asterix24/nixi-clock/hardware/kicad/main.kicad_sch

## KiCad design hardware/kicad/main.kicad_sch (2026-05-16)

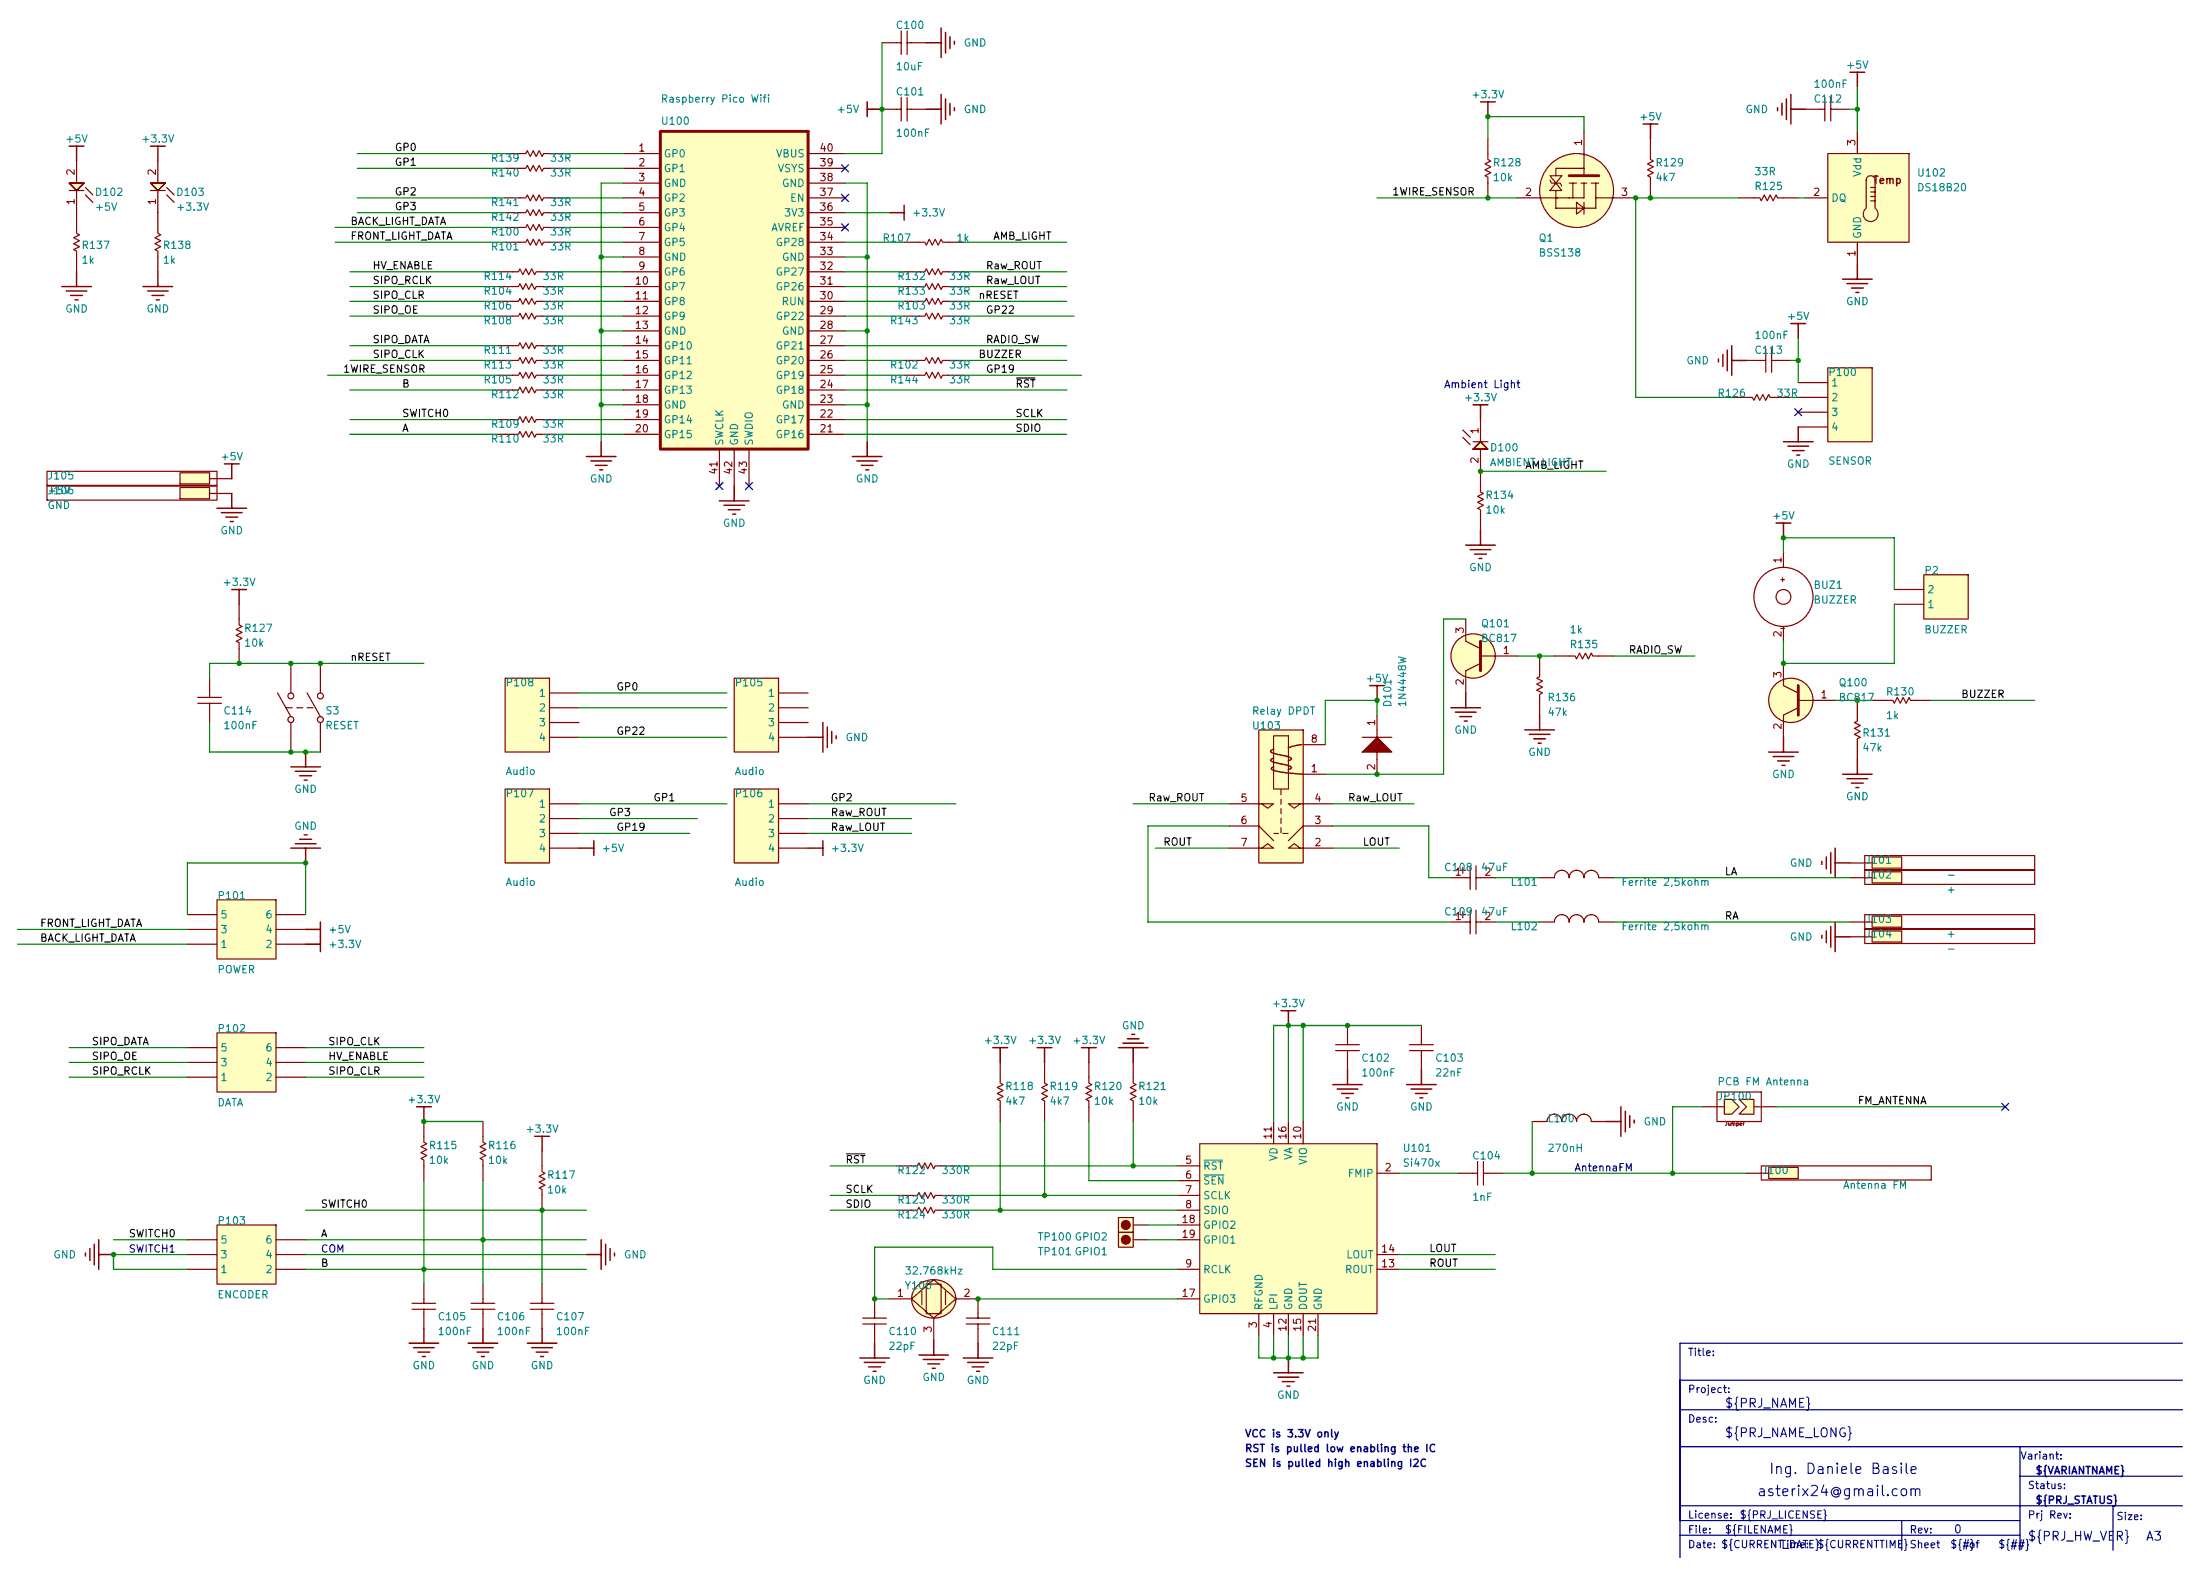
[picture p26: schematic main.kicad_sch]

Parts:
BUZ1: BUZZER; buzzer_14mm_thd
C100: 10uF; 0603_[1608]
C101, C102, C105, C106, C107, C112, C113, C114: 100nF; 0603_[1608]
C103: 22nF; 0603_[1608]
C104: 1nF; 0603_[1608]
C108, C109: 47uF; [7343]_CAP_TAN_1P_2N
C110, C111: 22pF; 0603_[1608]
D100: AMBIENT LIGHT; R5_LED_THD_A2-K1
D101: 1N4448W; SOD-123_K1-A2
D102: +5V; 0603_[1608]_K1-A2_LED
D103: +3.3V; 0603_[1608]_K1-A2_LED
J100: Antenna FM; SMD_PIN_2x5MM
J101, J104: -; SMD_PIN_2x5MM
J102, J103: +; SMD_PIN_2x5MM
J105: +5V; SMD_PIN_2x5MM
J106: GND; SMD_PIN_2x5MM
JP100: PCB FM Antenna; 0603_[1608]_JUMPER
L100: 270nH; 0603_[1608]
L101, L102: Ferrite 2,5kohm; 0603_[1608]
P2: BUZZER; HEADER_1X2_2.54MM_THD
P100: SENSOR; HEADER_1X4_2.54MM_THD
P101: POWER; SOCKET_2x3_2.54mm_THD
P102: DATA; SOCKET_2x3_2.54mm_THD
P103: ENCODER; SOCKET_2x3_2.54mm_THD
P105, P106, P107, P108: Audio; HEADER_1X4_2.54MM_THD
Q1: BSS138; SOT-23
Q100, Q101: BC817; SOT-23
R100, R101, R102, R103, R104, R105, R106, R108, R109, R110, R111, R112, R113, R114, R125, R126, R132, R133, R139, R140, R141, R142, R143, R144: 33R; 0603_[1608]
R107, R130, R135, R137, R138: 1k; 0603_[1608]
R115, R116, R117, R120, R121, R127, R128, R134: 10k; 0603_[1608]
R118, R119, R129: 4k7; 0603_[1608]
R122, R123, R124: 330R; 0603_[1608]
R131, R136: 47k; 0603_[1608]
S3: RESET; TACTILE_SWITCH_6x6MM_THD
TP100: GPIO2; TEST_POINT_THD_D1.6MM
TP101: GPIO1; TEST_POINT_THD_D1.6MM
U100: Raspberry Pico Wifi; RasberryPicoMod
U101: Si470x; QFN-50P-20_PAD
U102: DS18B20; TO-92
U103: Relay DPDT; RELAYS_DPST_THD_6x10_5.08mm
Y100: 32.768kHz; CRISTAL_R26_PAD

Connections:
1WIRE_SENSOR: Q1.2 (S), R105.2, R128.2
A: C106.2, P103.6, R110.2, R116.2
AMB_LIGHT: D100.2 (A), R107.1, R134.1
B: C105.2, P103.2, R112.2, R115.2
BACK_LIGHT_DATA: P101.1, R100.2
BUZZER: R102.1, R130.1
FM_ANTENNA: JP100.2
FRONT_LIGHT_DATA: P101.3, R101.2
GP0: P108.1, R139.2
GP1: P107.1, R140.2
GP2: P106.1, R141.2
GP3: P107.2, R142.2
GP19: P107.3, R144.1
GP22: P108.4, R143.1
HV_ENABLE: P102.4, R114.2
LA: J102.1, L101.2
LOUT: U101.14 (LOUT), U103.2
unnamed: BUZ1.1, P2.2
unnamed: BUZ1.2, P2.1, Q100.3
unnamed: C100.1, C101.1, U100.40 (VBUS)
unnamed: C102.2, C103.2, U101.10 (VIO), U101.11 (VD), U101.16 (VA)
unnamed: C104.1, U101.2 (FMIP)
unnamed: C104.2, J100.1, JP100.1, L100.1
unnamed: C108.1, U103.3
unnamed: C108.2, L101.1
unnamed: C109.1, U103.6
unnamed: C109.2, L102.1
unnamed: C110.2, U101.9 (RCLK), Y100.1
unnamed: C111.2, U101.17 (GPIO3), Y100.2
unnamed: C112.1, U102.3 (Vdd)
unnamed: C113.1, P100.1
unnamed: C114.1, S3.1 (COMMON1), S3.2 (COMMON2)
unnamed: D101.1 (K), U103.8
unnamed: D101.2 (A), Q101.3, U103.1 (T1)
unnamed: D102.1 (K), R137.2
unnamed: D103.1 (K), R138.2
unnamed: P100.2, R126.1
unnamed: P101.5, P101.6
unnamed: P103.1, P103.3
unnamed: Q1.1 (G), R128.1
unnamed: Q1.3 (D), R125.2, R126.2, R129.2
unnamed: Q100.1, R130.2, R131.2
unnamed: Q101.1, R135.2, R136.2
unnamed: R100.1, U100.6 (GP4)
unnamed: R101.1, U100.7 (GP5)
unnamed: R102.2, U100.26 (GP20)
unnamed: R103.2, U100.30 (RUN)
unnamed: R104.1, U100.10 (GP7)
unnamed: R105.1, U100.16 (GP12)
unnamed: R106.1, U100.11 (GP8)
unnamed: R107.2, U100.34 (GP28)
unnamed: R108.1, U100.12 (GP9)
unnamed: R109.1, U100.19 (GP14)
unnamed: R110.1, U100.20 (GP15)
unnamed: R111.1, U100.14 (GP10)
unnamed: R112.1, U100.17 (GP13)
unnamed: R113.1, U100.15 (GP11)
unnamed: R114.1, U100.9 (GP6)
unnamed: R115.1, R116.1
unnamed: R118.2, R124.1, U101.8 (SDIO)
unnamed: R119.2, R123.1, U101.7 (SCLK)
unnamed: R120.2, U101.6 (~SEN)
unnamed: R121.2, R122.1, U101.5 (~RST)
unnamed: R125.1, U102.2 (DQ)
unnamed: R132.2, U100.32 (GP27)
unnamed: R133.2, U100.31 (GP26)
unnamed: R139.1, U100.1 (GP0)
unnamed: R140.1, U100.2 (GP1)
unnamed: R141.1, U100.4 (GP2)
unnamed: R142.1, U100.5 (GP3)
unnamed: R143.2, U100.29 (GP22)
unnamed: R144.2, U100.25 (GP19)
unnamed: TP100.1, U101.18 (GPIO2)
unnamed: TP101.1, U101.19 (GPIO1)
unnamed: U100.3 (GND), U100.8 (GND), U100.13 (GND), U100.18 (GND)
unnamed: U100.23 (GND), U100.28 (GND), U100.33 (GND), U100.38 (GND)
unnamed: U101.3 (RFGND), U101.4 (LPI), U101.12 (GND), U101.15 (DOUT), U101.21 (GND)
RA: J103.1, L102.2
RADIO_SW: R135.1, U100.27 (GP21)
ROUT: U101.13 (ROUT), U103.7
Raw_LOUT: P106.3, R133.1, U103.4
Raw_ROUT: P106.2, R132.1, U103.5
SCLK: R123.2, U100.22 (GP17)
SDIO: R124.2, U100.21 (GP16)
SIPO_CLK: P102.6, R113.2
SIPO_CLR: P102.2, R106.2
SIPO_DATA: P102.5, R111.2
SIPO_OE: P102.3, R108.2
SIPO_RCLK: P102.1, R104.2
SWITCH0: C107.2, P103.5, R109.2, R117.2
nRESET: C114.2, R103.1, R127.2, S3.3 (NO1), S3.4 (NO2)
~RST: R122.2, U100.24 (GP18)

Notes on the sheet:
${##}
COM
VCC is 3.3V only
asterix24@gmail.com
${#}
${REVISION}
Sheet
${CURRENT_DATE}
${PRJ_LICENSE}
${VARIANTNAME}
File:
Project:
SEN is pulled high enabling I2C
${FILENAME}
Ing. Daniele Basile
AntennaFM
${PRJ_NAME}
Status:
Variant:
Desc:
${PRJ_NAME_LONG}
Date:
SWITCH1
${TITLE}
${CURRENTTIME}
Title:
Time:
Ambient Light
${PRJ_STATUS}
Size:
Rev:
RST is pulled low enabling the IC
Prj Rev:
${PRJ_HW_VER}
License:
