asterix24/nixi-clock/hardware/kicad/supply.kicad_sch

## KiCad design hardware/kicad/supply.kicad_sch (2026-05-16)

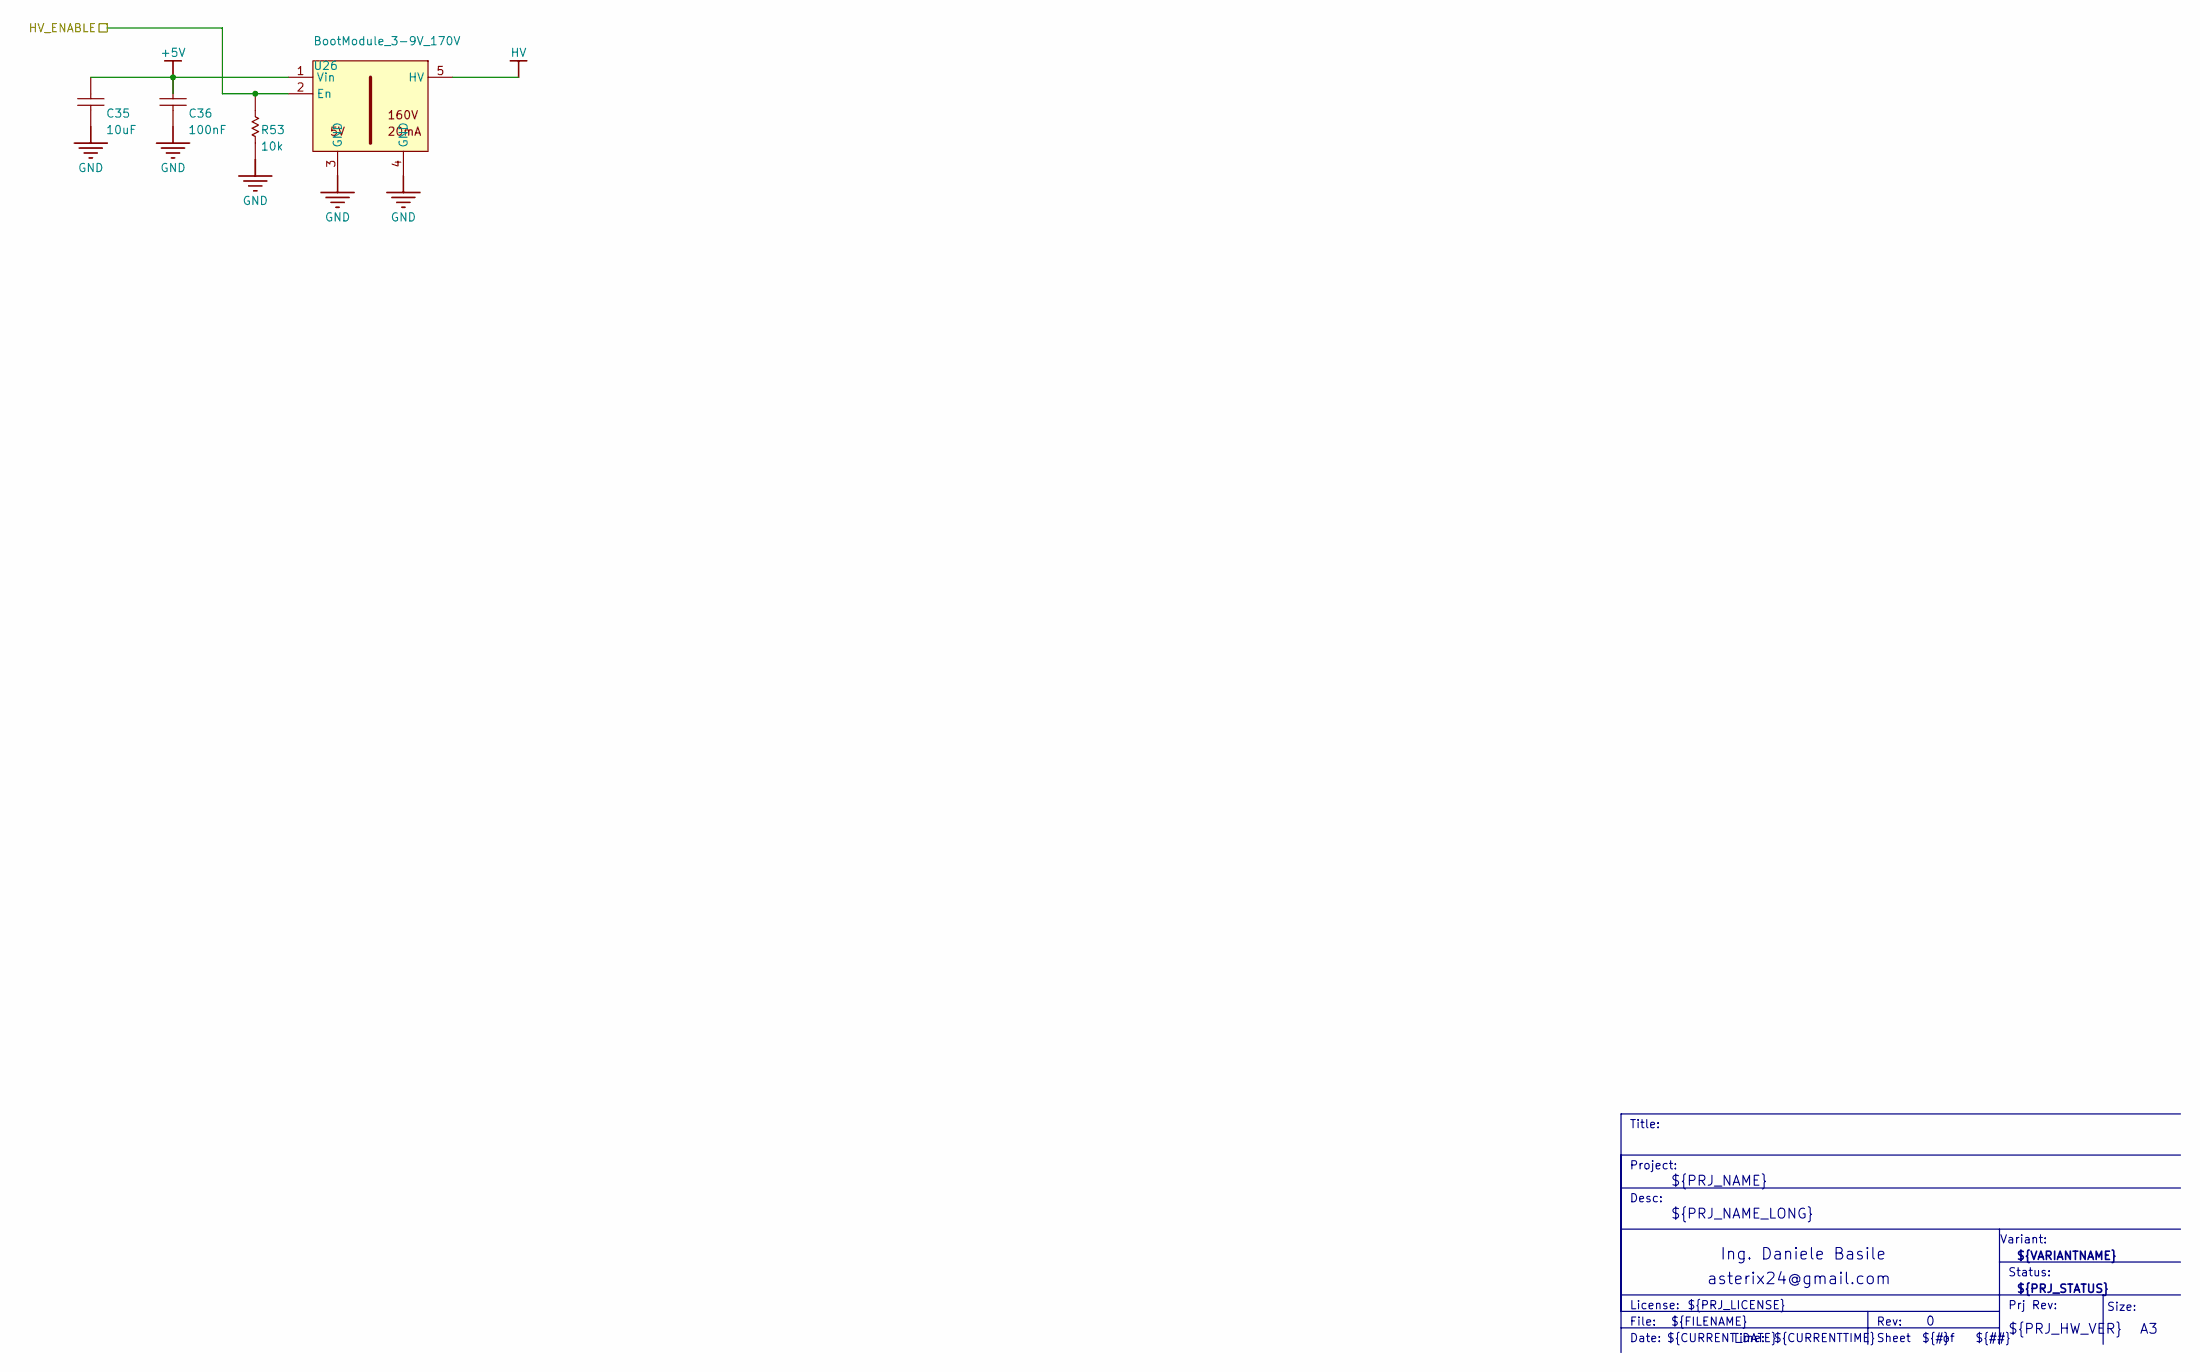
[picture p27: schematic supply.kicad_sch]

Parts:
C35: 10uF; 0603_[1608]
C36: 100nF; 0603_[1608]
R53: 10k; 0603_[1608]
U26: BootModule_3-9V_170V; BoostModule

Connections:
HV_ENABLE: R53.2, U26.2 (En)
unnamed: C35.2, C36.2, U26.1 (Vin)

Notes on the sheet:
${PRJ_NAME}
Desc:
${PRJ_LICENSE}
Date:
${##}
Size:
Rev:
${PRJ_NAME_LONG}
License:
${PRJ_HW_VER}
Sheet
${FILENAME}
${CURRENT_DATE}
Variant:
${REVISION}
${PRJ_STATUS}
${#}
Ing. Daniele Basile
asterix24@gmail.com
${VARIANTNAME}
Time:
Project:
Title:
${TITLE}
File:
Prj Rev:
Status:
${CURRENTTIME}
