asterix24/nixi-clock/hardware/kicad/tube.kicad_sch

## KiCad design hardware/kicad/tube.kicad_sch (2026-05-16)

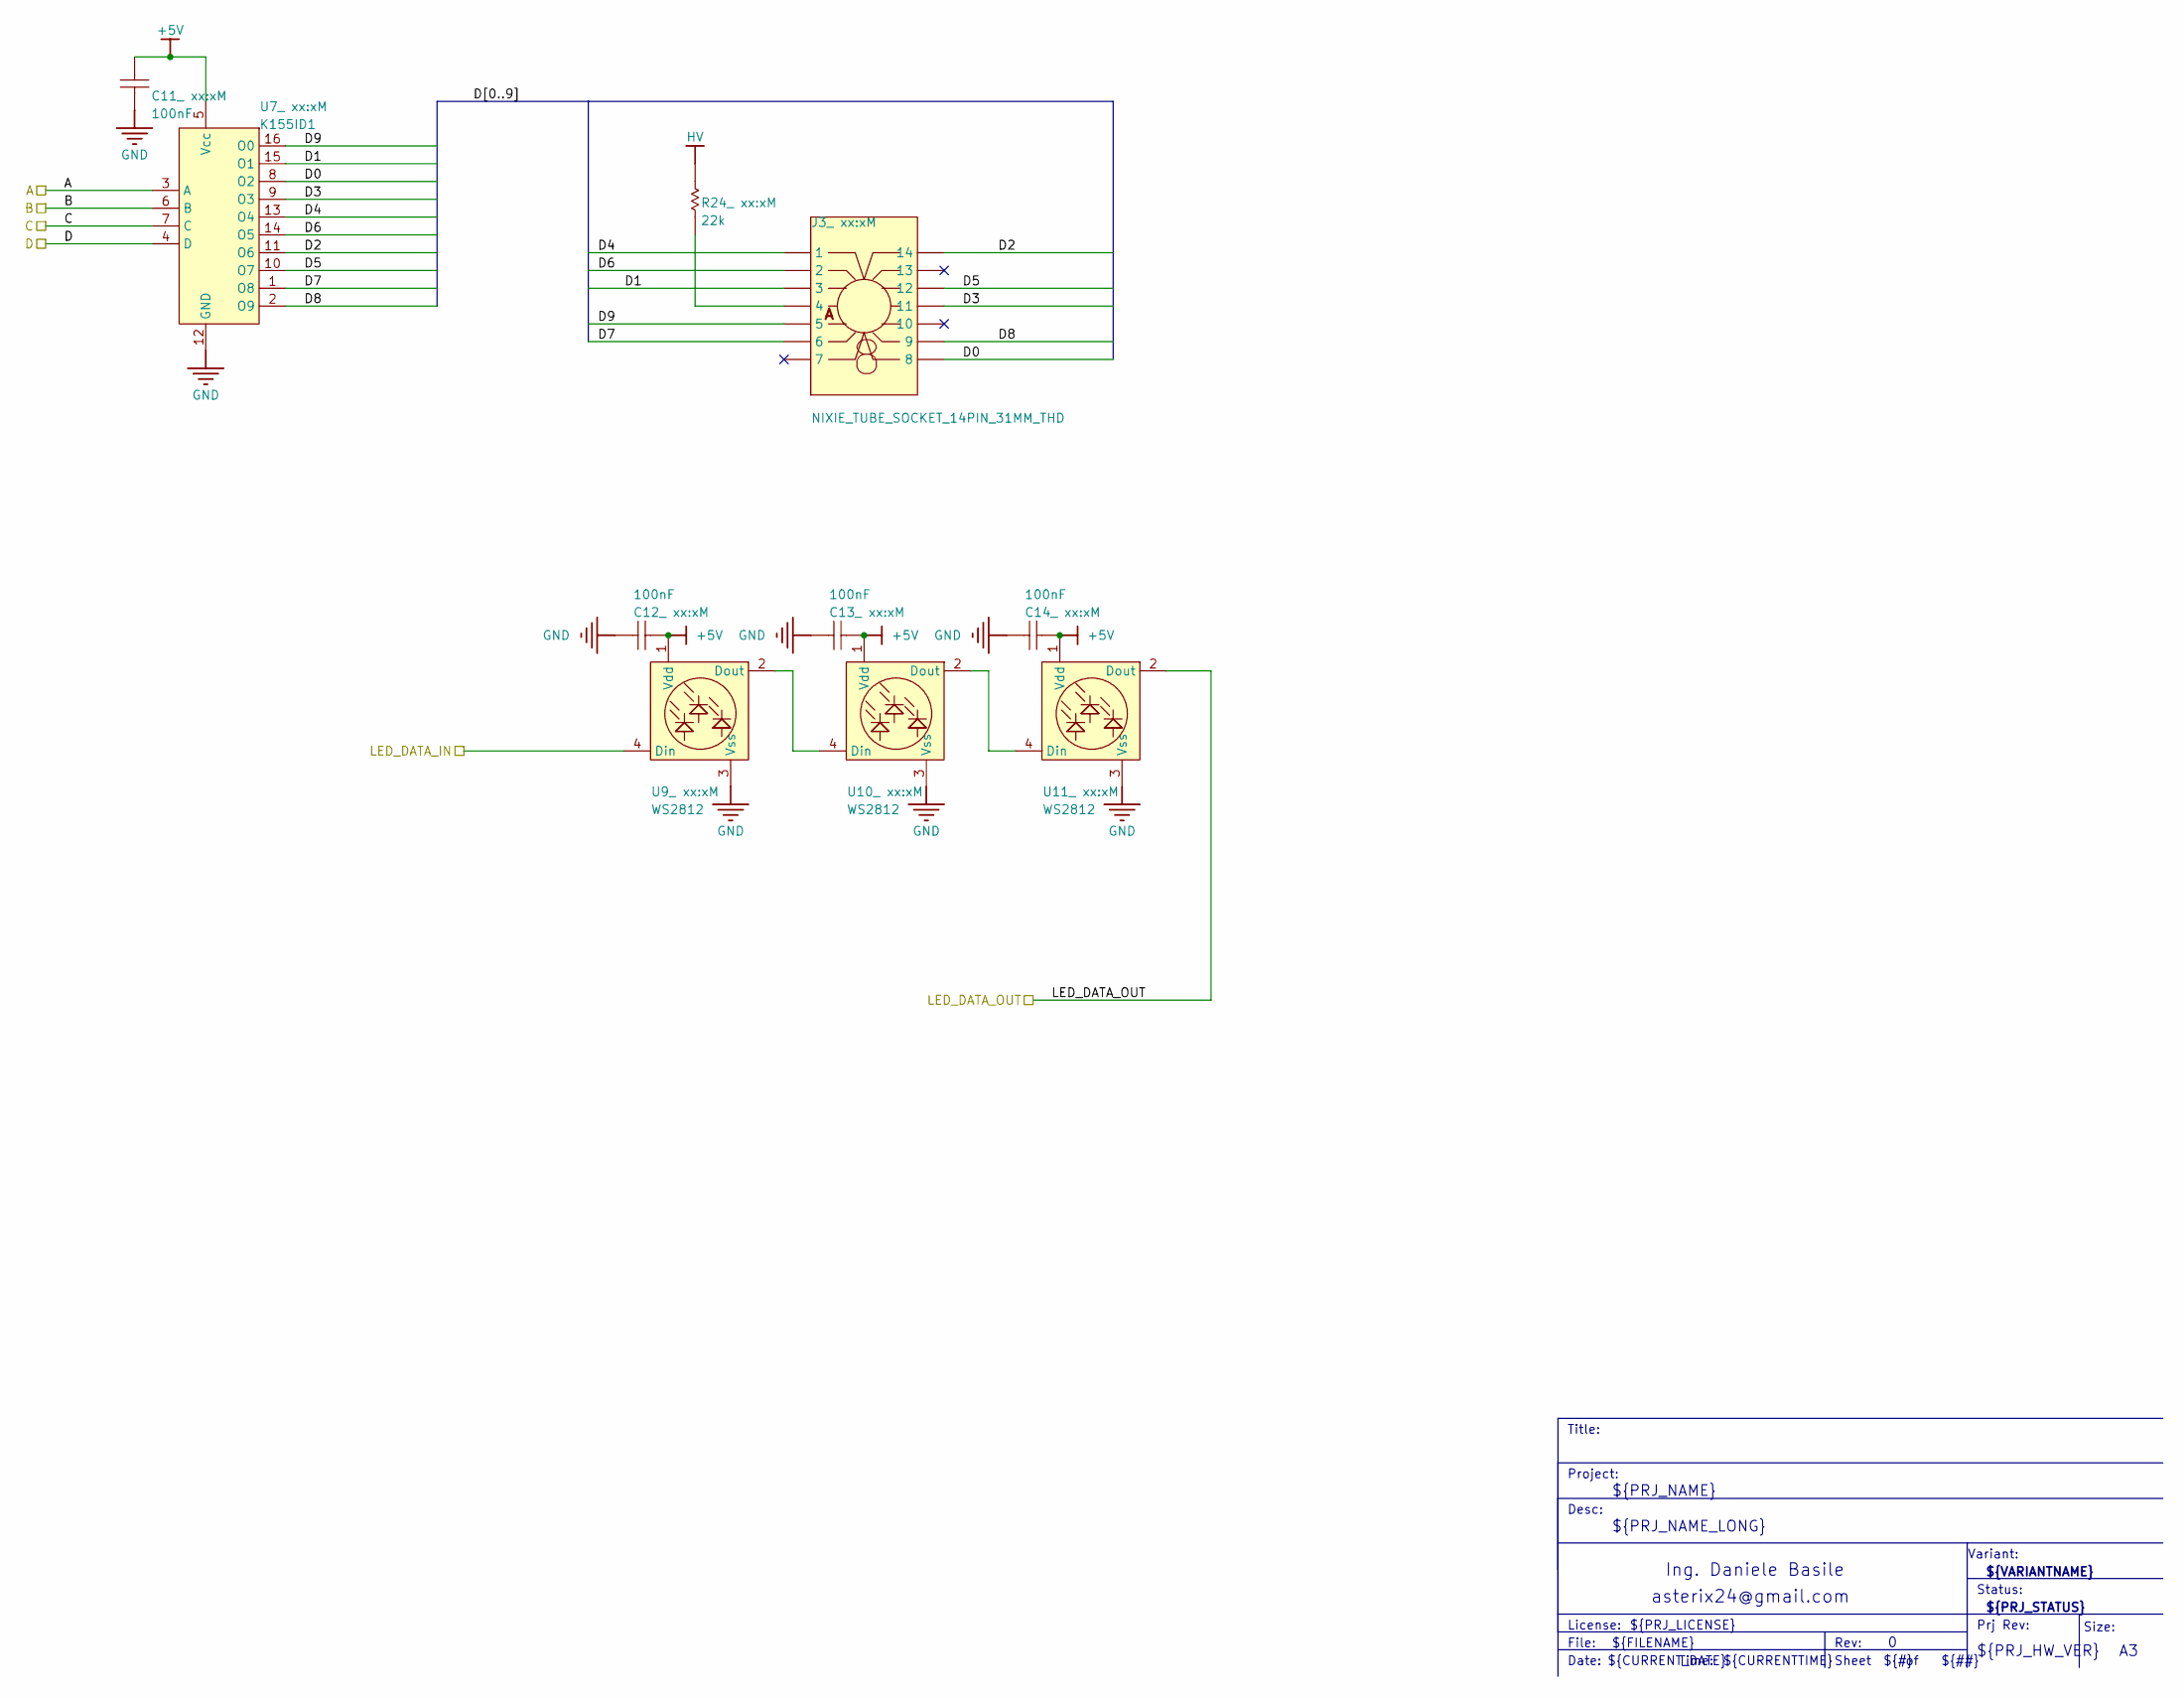
[picture p28: schematic tube.kicad_sch]

Parts:
C11_ xx:xM, C12_ xx:xM, C13_ xx:xM, C14_ xx:xM: 100nF; 0603_[1608]
J3_ xx:xM: NIXIE_TUBE_SOCKET_14PIN_31MM_THD; SOCKET_NIXI_TUBE
R24_ xx:xM: 22k; AXIAL 10mm
U7_ xx:xM: K155ID1; DIP-16_THD
U9_ xx:xM, U10_ xx:xM, U11_ xx:xM: WS2812; LED_PLCC_RGB_4P_1010

Connections:
A: U7_ xx:xM.3 (A)
B: U7_ xx:xM.6 (B)
C: U7_ xx:xM.7 (C)
D: U7_ xx:xM.4 (D)
D0: J3_ xx:xM.8, U7_ xx:xM.8 (O2)
D1: J3_ xx:xM.3, U7_ xx:xM.15 (O1)
D2: J3_ xx:xM.14, U7_ xx:xM.11 (O6)
D3: J3_ xx:xM.11, U7_ xx:xM.9 (O3)
D4: J3_ xx:xM.1, U7_ xx:xM.13 (O4)
D5: J3_ xx:xM.12, U7_ xx:xM.10 (O7)
D6: J3_ xx:xM.2, U7_ xx:xM.14 (O5)
D7: J3_ xx:xM.6, U7_ xx:xM.1 (O8)
D8: J3_ xx:xM.9, U7_ xx:xM.2 (O9)
D9: J3_ xx:xM.5, U7_ xx:xM.16 (O0)
LED_DATA_IN: U9_ xx:xM.4 (Din)
LED_DATA_OUT: U11_ xx:xM.2 (Dout)
unnamed: C11_ xx:xM.2, U7_ xx:xM.5 (Vcc)
unnamed: C12_ xx:xM.2, U9_ xx:xM.1 (Vdd)
unnamed: C13_ xx:xM.2, U10_ xx:xM.1 (Vdd)
unnamed: C14_ xx:xM.2, U11_ xx:xM.1 (Vdd)
unnamed: J3_ xx:xM.4, R24_ xx:xM.1
unnamed: U10_ xx:xM.2 (Dout), U11_ xx:xM.4 (Din)
unnamed: U9_ xx:xM.2 (Dout), U10_ xx:xM.4 (Din)

Notes on the sheet:
asterix24@gmail.com
File:
${REVISION}
License:
Title:
Desc:
${CURRENTTIME}
${PRJ_LICENSE}
${TITLE}
Prj Rev:
Variant:
${CURRENT_DATE}
${VARIANTNAME}
Time:
Date:
Sheet
Project:
${PRJ_HW_VER}
${FILENAME}
${#}
Ing. Daniele Basile
Rev:
${PRJ_STATUS}
Status:
${PRJ_NAME_LONG}
${PRJ_NAME}
Size:
${##}
